bpatern/EIKII_multifunctional_artsprojector/projector_code/graphics.h

static const unsigned char image_sleepyeyes_bits[] = {0x00,0x00,0x00,0x04,0x04,0x00,0x00,0x10,0x02,0x00,0x00,0x04,0x04,0x00,0x00,0x10,0x03,0x00,0x00,0x04,0x04,0x00,0x00,0x10,0x03,0x00,0x00,0x04,0x04,0x00,0x00,0x18,0x03,0x00,0x00,0x06,0x04,0x00,0x00,0x08,0x02,0x00,0x00,0x02,0x04,0x00,0x00,0x08,0x06,0x00,0x00,0x03,0x0c,0x00,0x00,0x04,0x0c,0x00,0x80,0x01,0x0c,0x00,0x00,0x06,0x1c,0x00,0xc0,0x00,0x0c,0x00,0x00,0x03,0xf8,0x00,0x60,0x00,0x1c,0x00,0x80,0x03,0xf0,0x07,0x3c,0x00,0x1c,0x00,0xc0,0x00,0xc0,0xff,0x0f,0x00,0x3c,0x00,0x30,0x00,0x00,0xe0,0x00,0x00,0xf8,0x00,0x1e,0x00,0x00,0x00,0x00,0x00,0xf0,0xff,0x07,0x00,0x00,0x00,0x00,0x00,0xc0,0x3f,0x00,0x00};
static const unsigned char image_zzz1_bits[] = {0x00,0x00,0x00,0x01,0x00,0x00,0xc0,0x01,0x00,0x00,0x60,0x01,0x00,0x00,0xb8,0x00,0x00,0x00,0x80,0x00,0x00,0x00,0xc0,0x20,0x00,0x07,0x40,0x38,0x80,0x07,0x60,0x0c,0xe0,0x02,0x20,0x06,0x30,0xc2,0x20,0x03,0x00,0x63,0xb0,0x01,0x00,0x31,0x70,0x00,0x00,0x1d,0x30,0x00,0x00,0x07,0x00,0x00,0x00,0x01,0x00,0x00,0x00,0x00,0x00,0x00,0x00,0x00,0x00,0x00,0x00,0x00,0x00,0x00,0x30,0x00,0x00,0x00,0x38,0x02,0x00,0x00,0x3e,0x03,0x00,0x00,0x93,0x01,0x00,0x00,0xd0,0x00,0x00,0x00,0x30,0x00,0x00,0x00};
static const unsigned char image_zzz2_bits[] = {0x00,0x00,0x80,0x03,0x00,0x00,0xe0,0x03,0x00,0x00,0x18,0x01,0x00,0x00,0x87,0x01,0x00,0x00,0x80,0x00,0x00,0x00,0xc0,0x00,0x00,0x00,0x40,0x00,0x00,0x00,0x40,0x00,0x00,0x00,0x40,0x00,0x00,0x00,0x20,0x00,0x00,0x00,0x20,0x00,0x00,0x00,0x20,0x70,0x00,0x00,0x10,0x1e,0x00,0x00,0x90,0x03,0x00,0x00,0xf0,0x00,0x00,0x00,0x00,0x00,0x00,0x80,0x07,0x00,0x00,0xe0,0x02,0x00,0x00,0x30,0x02,0x00,0x00,0x00,0x02,0x00,0x00,0x00,0x03,0x00,0x00,0x00,0x01,0x00,0x00,0x00,0x19,0x00,0x30,0x80,0x0f,0x00,0x3c,0x80,0x03,0x00,0x27,0x00,0x00,0x00,0xa0,0x01,0x00,0x00,0xf0,0x00,0x00,0x00,0x30,0x00,0x00,0x00};

int flicker = 0;
int eyesPos = 0;
int eyesPosPrev = 0;
float eyesPosKeyF = 0;
  float eyesAnimPos = 0;

  int zzzPos = 0;
  int zzzPosPrev = 0;
  int zzzPosFrame = 0;
